nicholasgrummon/PC-Case/Pictures/Cover_Photo.jpeg

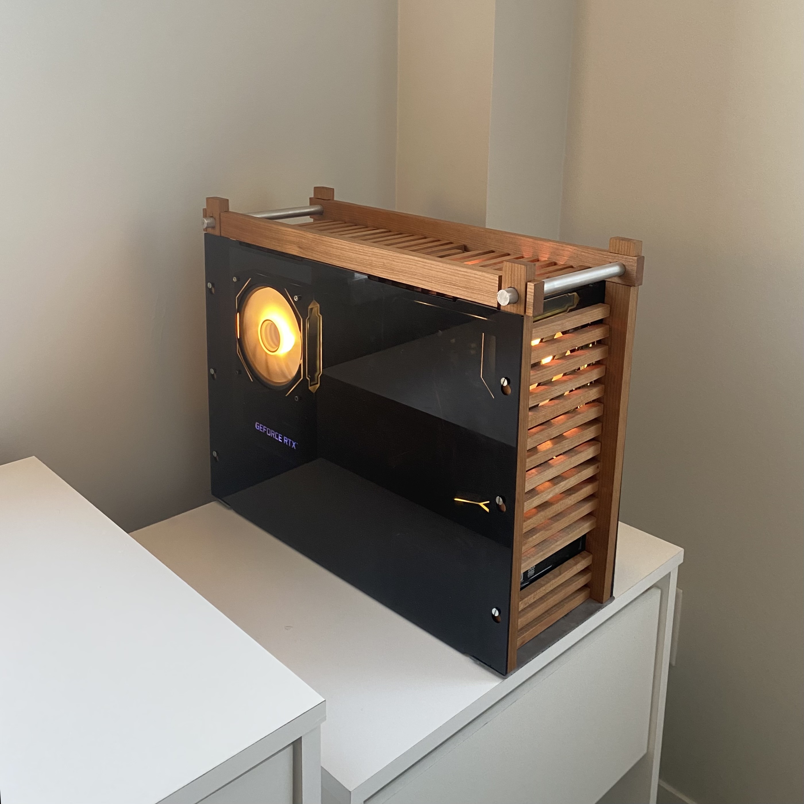
Pictures/Cover_Photo.jpeg
