nicholasgrummon/PC-Case/CADv3/PC-Case3.SLDASM

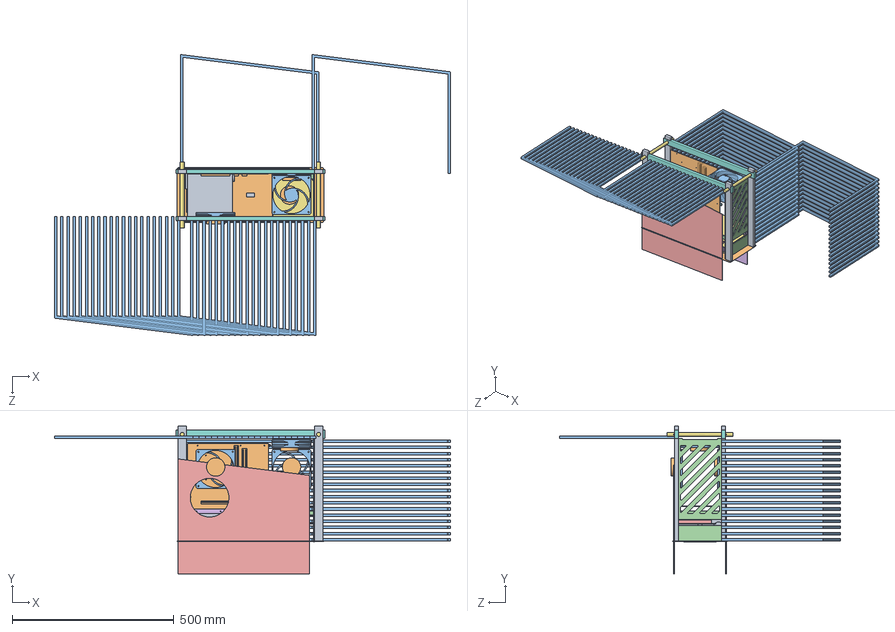
[picture p3: CAD file, 2026-05-30]
CADv3/PC-Case3.SLDASM
1225.5 x 457.2 x 869.7 mm
Base-plate
Frame-upright x 4
Frame-across x 2
Handle-rod x 2
Back-panel
Front-panel
Interface-panel
Wood-slat x 55
Motherboard
PSU
Bracket-across x 2
Hardware-Tray x 4
Hard-drive
SSD
CD-Drive
FAN BODY x 3
FAN BLADES x 3
GPU-support
