nicholasgrummon/PC-Case/CADv2/Frame-mock.SLDASM

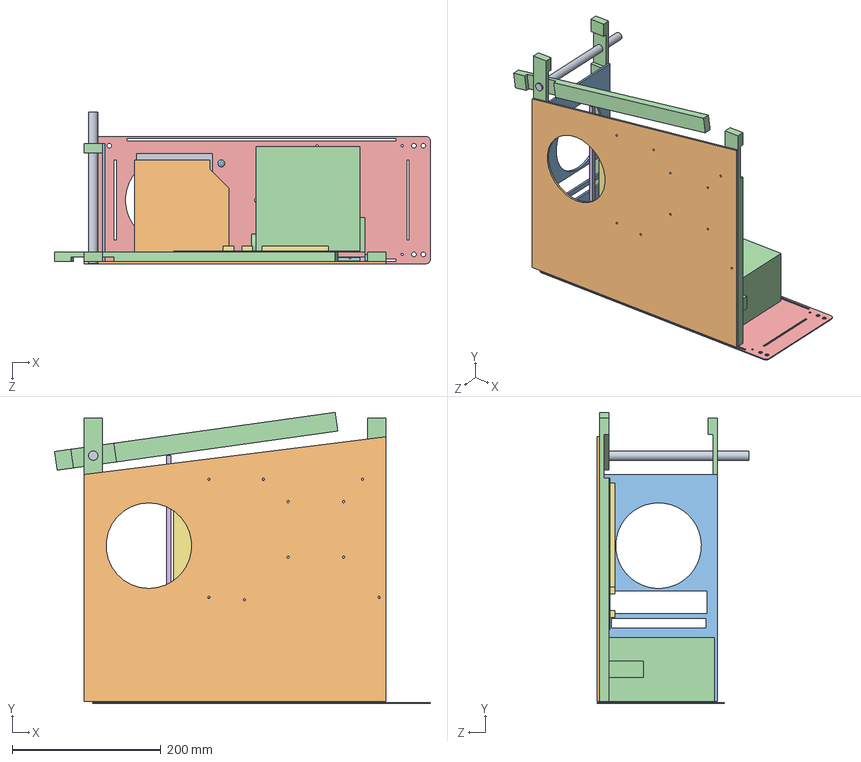
[picture p4: CAD file, 2026-05-30]
CADv2/Frame-mock.SLDASM
505.4 x 391.6 x 203.9 mm
Base-plate
Corner-slat x 4
Short-panel
Back-panel
Handle
Lbracket-short
Motherboard
Motherboard-upright-bracket x 2
Motherboard-across-bracket x 2
PSU
GPU-Post
CD-Drive
Hard-drive
