nicholasgrummon/PC-Case/CADv1/PC-Case.SLDASM

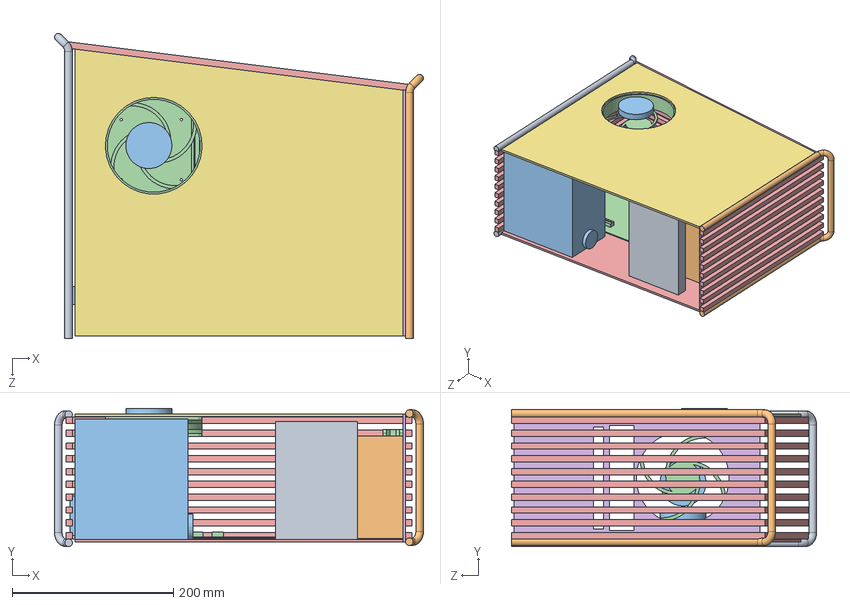
[picture p5: CAD file, 2026-05-30]
CADv1/PC-Case.SLDASM
457.3 x 171.1 x 378.3 mm
Back-panel
Motherboard
PSU
CD-Drive
Hard-drive
SSD
Front-panel
Short-panel
Wood-slat x 10
FAN BODY x 3
FAN BLADES x 3
Short-frame
Tall-frame
