nicholasgrummon/PC-Case/CADv1/Acrylic-layout.SLDASM

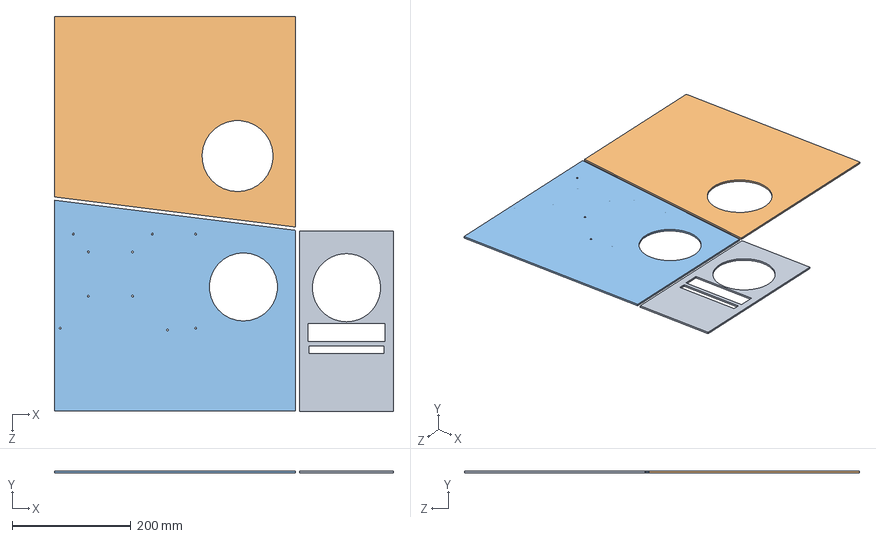
[picture p6: CAD file, 2026-05-30]
CADv1/Acrylic-layout.SLDASM
572.2 x 3.17 x 667.2 mm
Back-panel
Front-panel
Short-panel
