nicholasgrummon/PC-Case/CADv4/CPU.SLDPRT

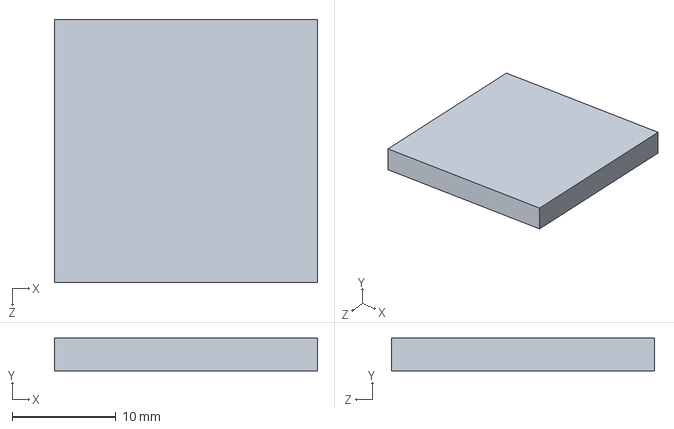
[picture p20: CAD file, 2026-05-30]
CADv4/CPU.SLDPRT
25.4 x 3.17 x 25.4 mm
