nicholasgrummon/PC-Case/CADv1/Front-panel.SLDPRT

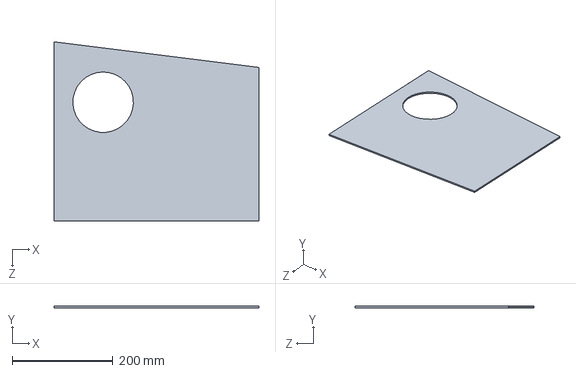
[picture p21: CAD file, 2026-05-30]
CADv1/Front-panel.SLDPRT
406.4 x 3.17 x 355.6 mm
