nicholasgrummon/PC-Case/CADv2/Motherboard-across-bracket.SLDPRT

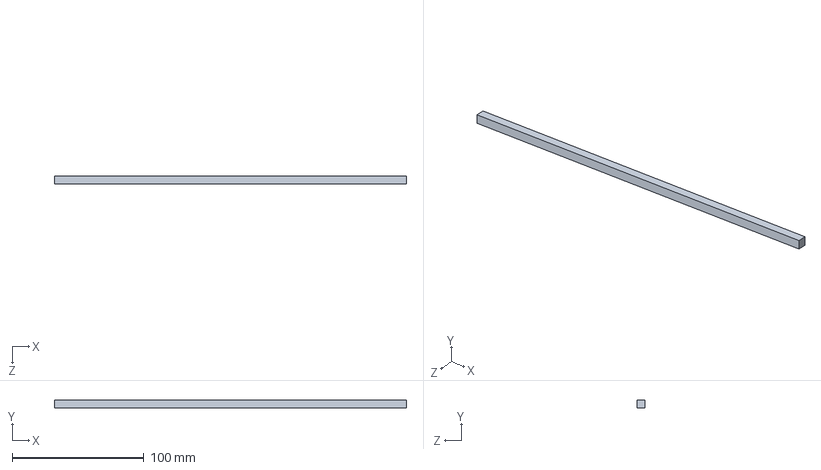
[picture p22: CAD file, 2026-05-30]
CADv2/Motherboard-across-bracket.SLDPRT
266.7 x 6.35 x 6.35 mm
