nicholasgrummon/PC-Case/CADv3/Base-plate.SLDPRT

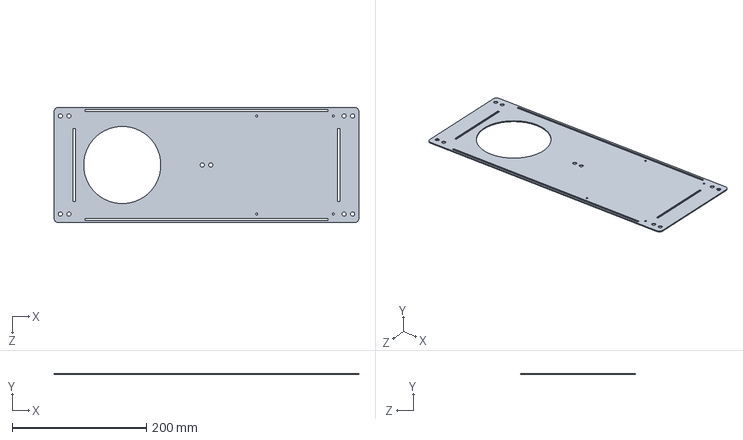
[picture p23: CAD file, 2026-05-30]
CADv3/Base-plate.SLDPRT
454.0 x 1.59 x 171.4 mm
