nicholasgrummon/PC-Case/CADv4/Unnamed-Solid001.iges

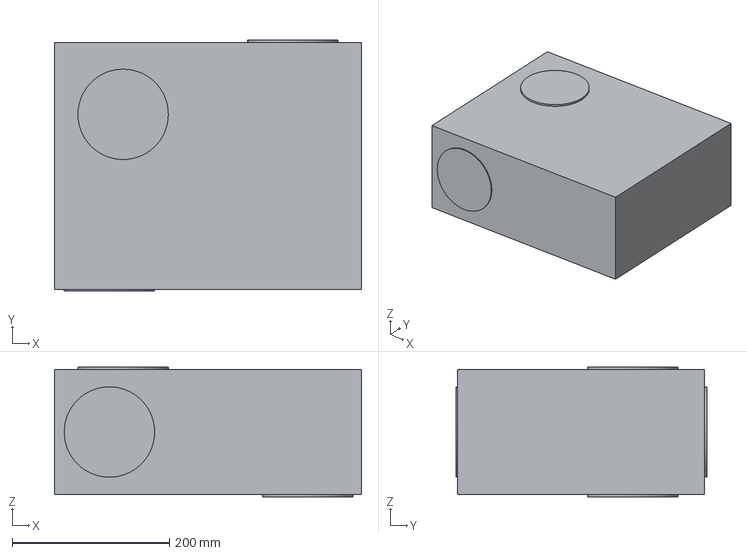
[picture p24: CAD file, 2026-05-30]
CADv4/Unnamed-Solid001.iges
390.5 x 319.1 x 165.1 mm
