nicholasgrummon/PC-Case/CADv2/GPU-Post.SLDPRT

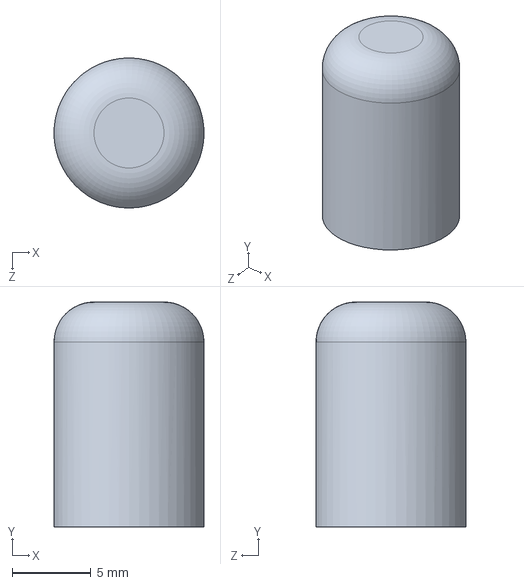
[picture p25: CAD file, 2026-05-30]
CADv2/GPU-Post.SLDPRT
9.52 x 14.3 x 9.53 mm
