nicholasgrummon/PC-Case/CADv3/GPU-support.SLDPRT

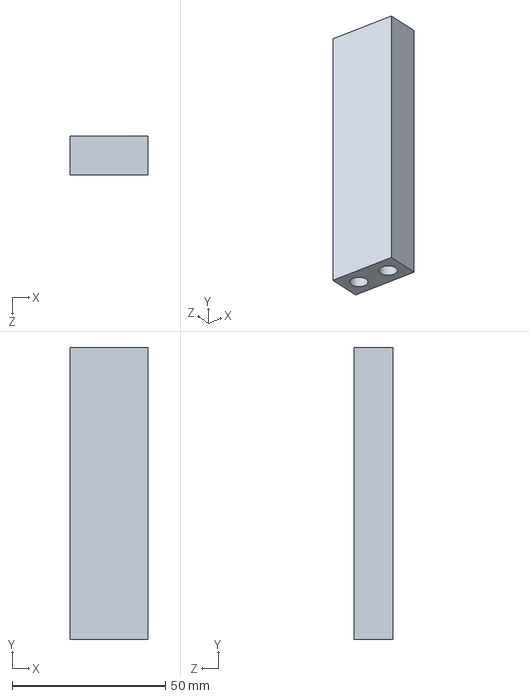
[picture p26: CAD file, 2026-05-30]
CADv3/GPU-support.SLDPRT
25.4 x 95.2 x 12.7 mm
