nicholasgrummon/PC-Case/CADv4/Back-panel-simple.SLDPRT

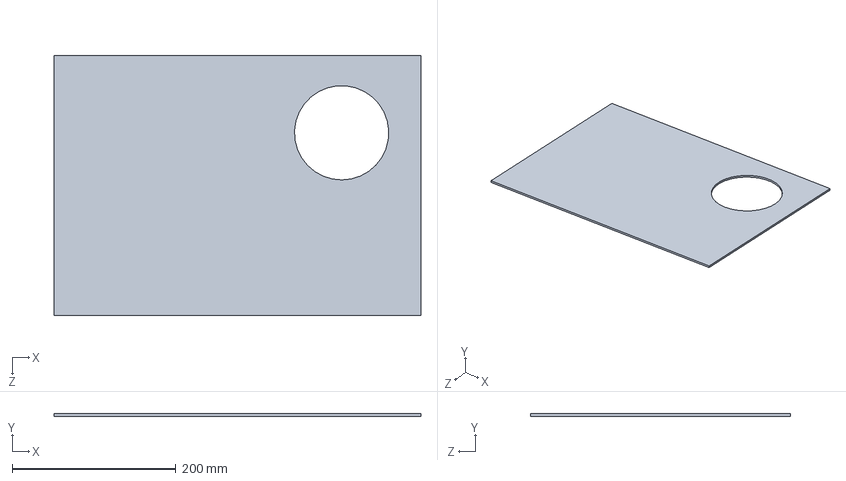
[picture p27: CAD file, 2026-05-30]
CADv4/Back-panel-simple.SLDPRT
447.7 x 3.17 x 317.5 mm
