nicholasgrummon/PC-Case/CADv1/Motherboard.SLDPRT

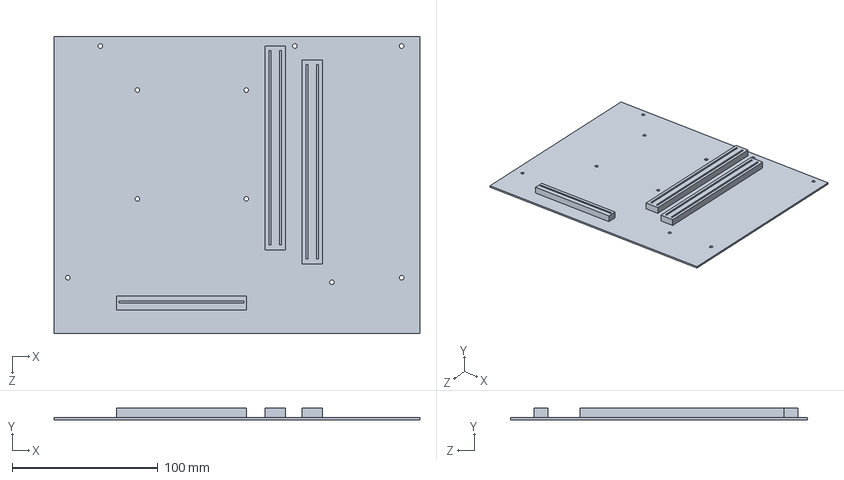
[picture p28: CAD file, 2026-05-30]
CADv1/Motherboard.SLDPRT
250.8 x 7.94 x 203.2 mm
