nicholasgrummon/PC-Case/CADv2/Wood-slat.SLDPRT

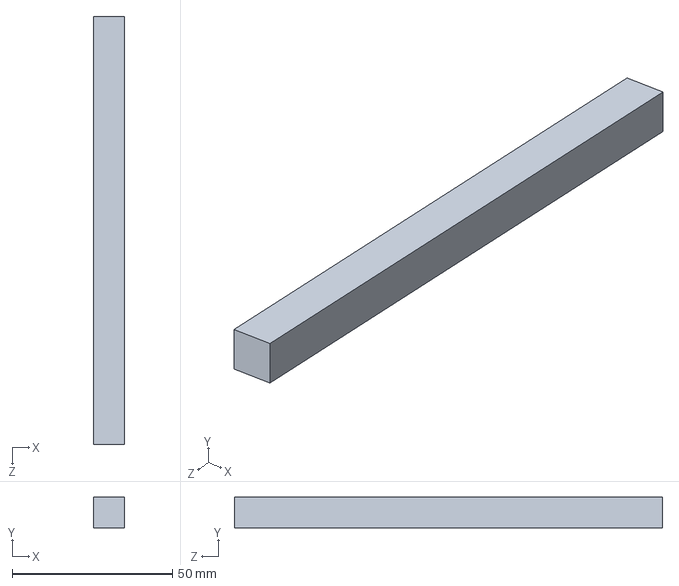
[picture p29: CAD file, 2026-05-30]
CADv2/Wood-slat.SLDPRT
9.53 x 9.53 x 133.4 mm
