nicholasgrummon/PC-Case/CADv3/Interface-panel.SLDPRT

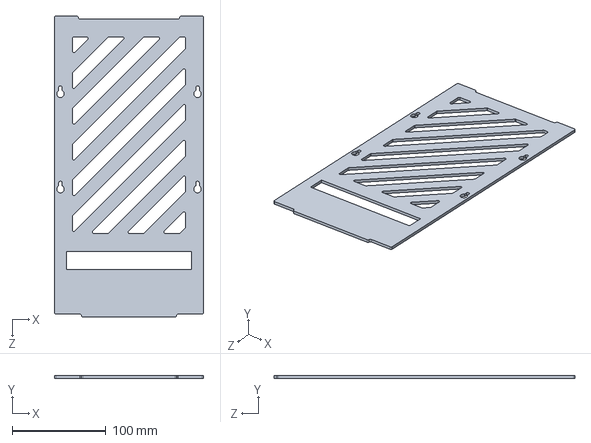
[picture p30: CAD file, 2026-05-30]
CADv3/Interface-panel.SLDPRT
158.8 x 3.17 x 320.7 mm
