nicholasgrummon/PC-Case/CADv2/Corner-slat.SLDPRT

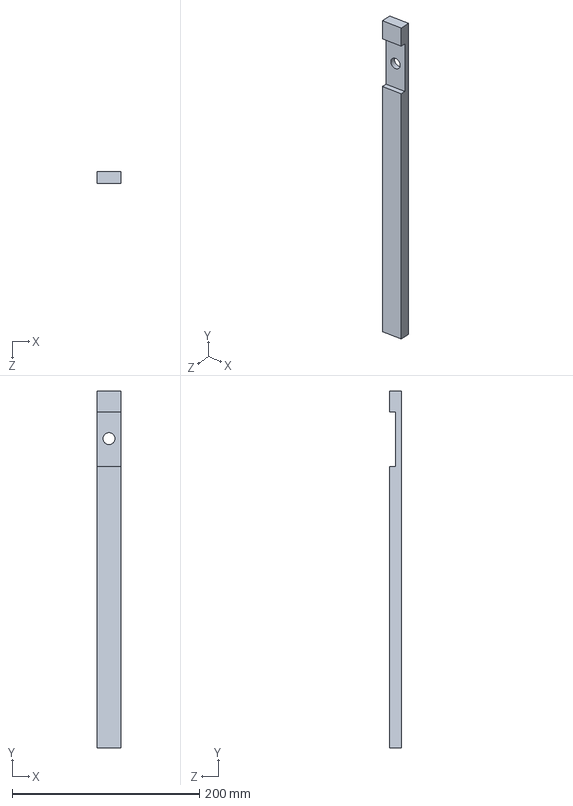
[picture p31: CAD file, 2026-05-30]
CADv2/Corner-slat.SLDPRT
25.4 x 381.0 x 12.7 mm
