nicholasgrummon/PC-Case/CADv3/Frame-across.SLDPRT

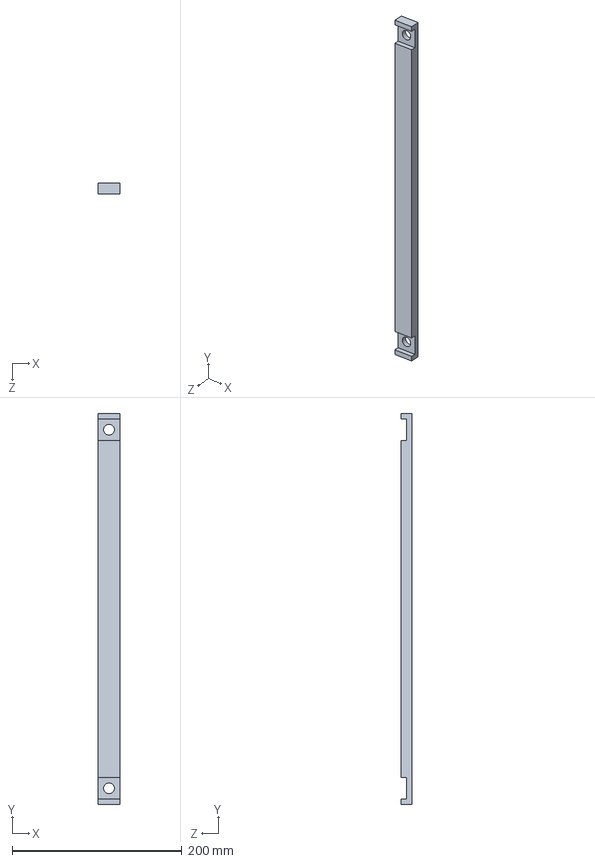
[picture p32: CAD file, 2026-05-30]
CADv3/Frame-across.SLDPRT
25.4 x 460.4 x 12.7 mm
