nicholasgrummon/PC-Case/CADv4/Frame-upright-simple.SLDPRT

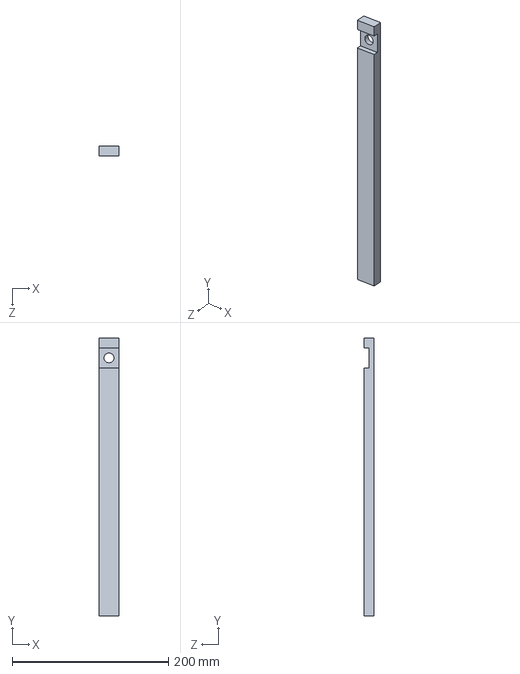
[picture p33: CAD file, 2026-05-30]
CADv4/Frame-upright-simple.SLDPRT
25.4 x 355.6 x 12.7 mm
