nicholasgrummon/PC-Case/CADv1/Short-frame.SLDPRT

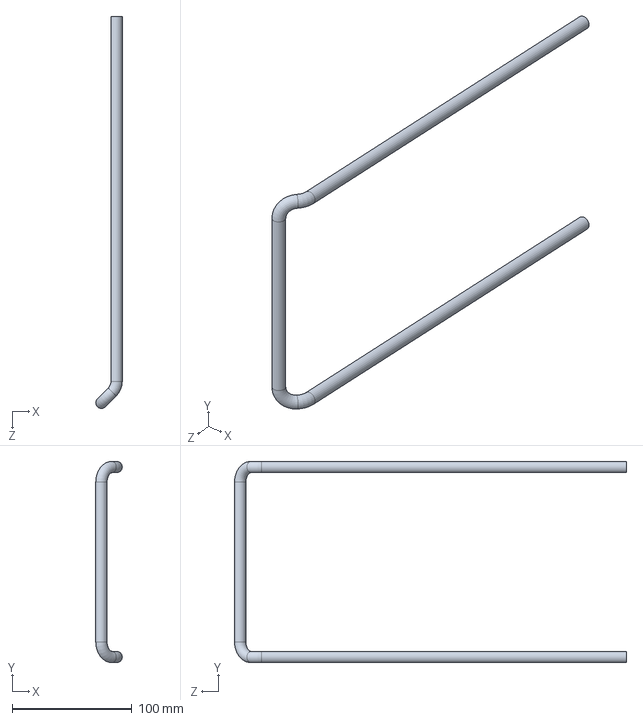
[picture p34: CAD file, 2026-05-30]
CADv1/Short-frame.SLDPRT
22.2 x 168.3 x 327.5 mm
