nicholasgrummon/PC-Case/CADv4/Air-volume.SLDPRT

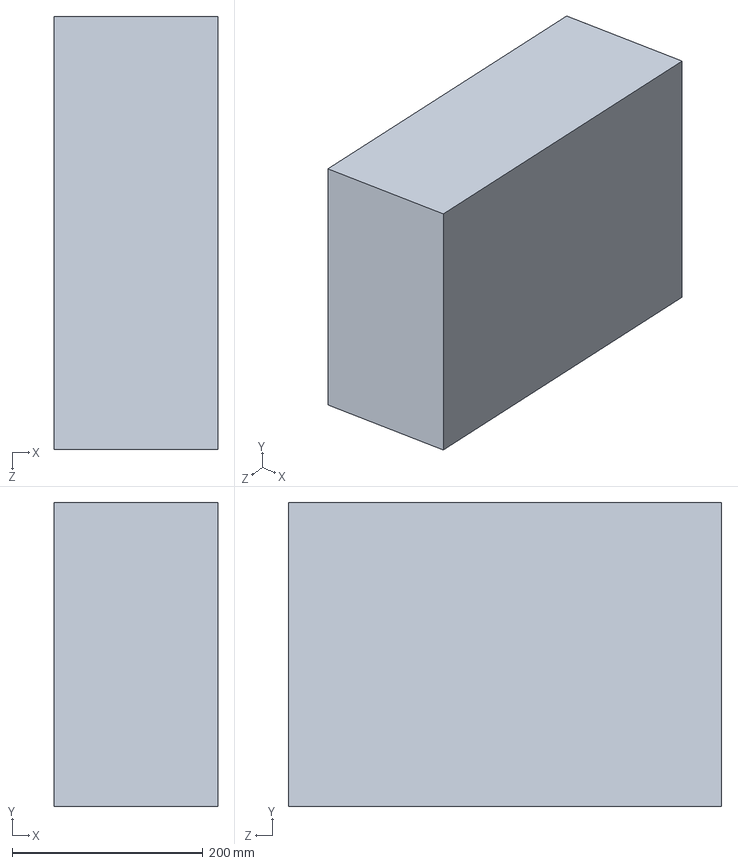
[picture p35: CAD file, 2026-05-30]
CADv4/Air-volume.SLDPRT
171.4 x 319.1 x 454.0 mm
