nicholasgrummon/PC-Case/CADv2/Hardware-Tray.SLDPRT

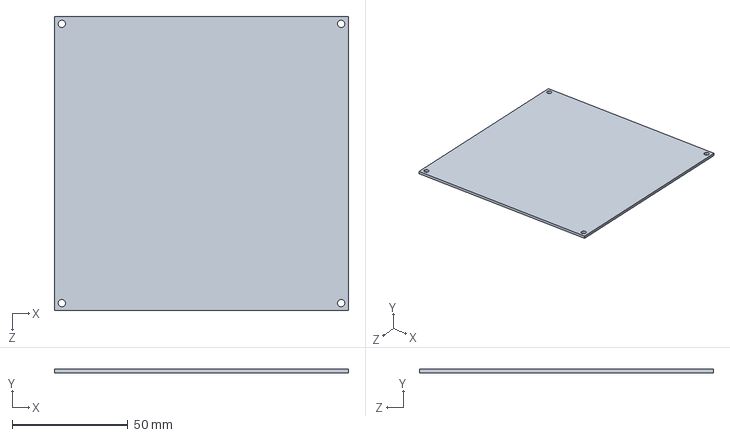
[picture p36: CAD file, 2026-05-30]
CADv2/Hardware-Tray.SLDPRT
127.0 x 1.59 x 127.0 mm
