nicholasgrummon/PC-Case/CADv2/Lbracket-short.SLDPRT

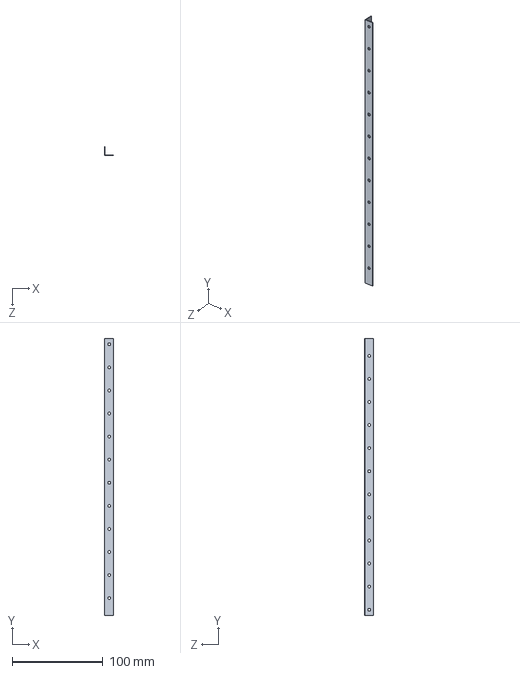
[picture p38: CAD file, 2026-05-30]
CADv2/Lbracket-short.SLDPRT
9.53 x 304.8 x 9.53 mm
