nicholasgrummon/PC-Case/CADv3/Frame-upright.SLDPRT

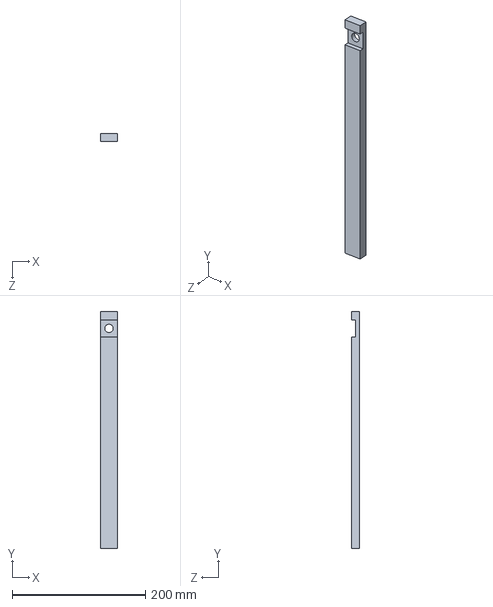
[picture p39: CAD file, 2026-05-30]
CADv3/Frame-upright.SLDPRT
25.4 x 355.6 x 12.7 mm
