nicholasgrummon/PC-Case/CADv4/PC-Case4.STEP

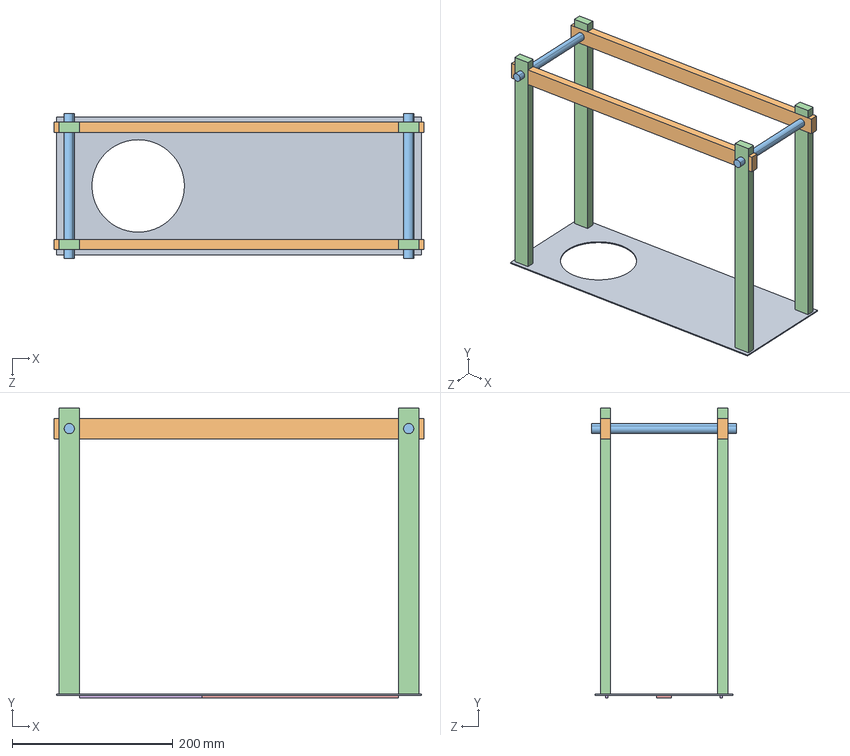
[picture p40: CAD file, 2026-05-30]
CADv4/PC-Case4.STEP
460.4 x 360.4 x 181.0 mm
Base-plate-simple
Frame-across x 2
Handle-rod-smooth x 2
Frame-upright-simple x 4
Bottom-brace
Side-brace x 2
