nicholasgrummon/PC-Case/CADv1/PSU.SLDPRT

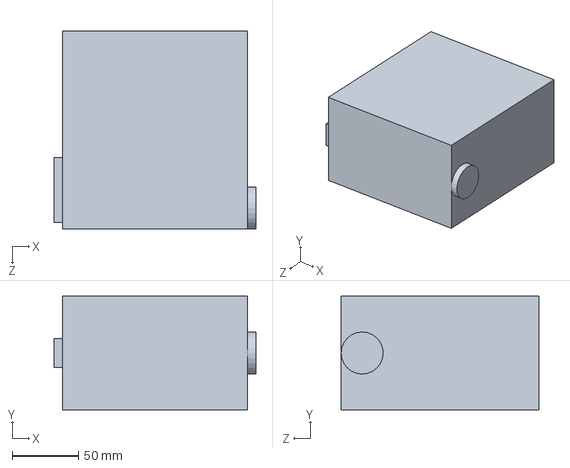
[picture p41: CAD file, 2026-05-30]
CADv1/PSU.SLDPRT
152.4 x 85.7 x 149.2 mm
