nicholasgrummon/PC-Case/CADv3/Hard-drive.SLDPRT

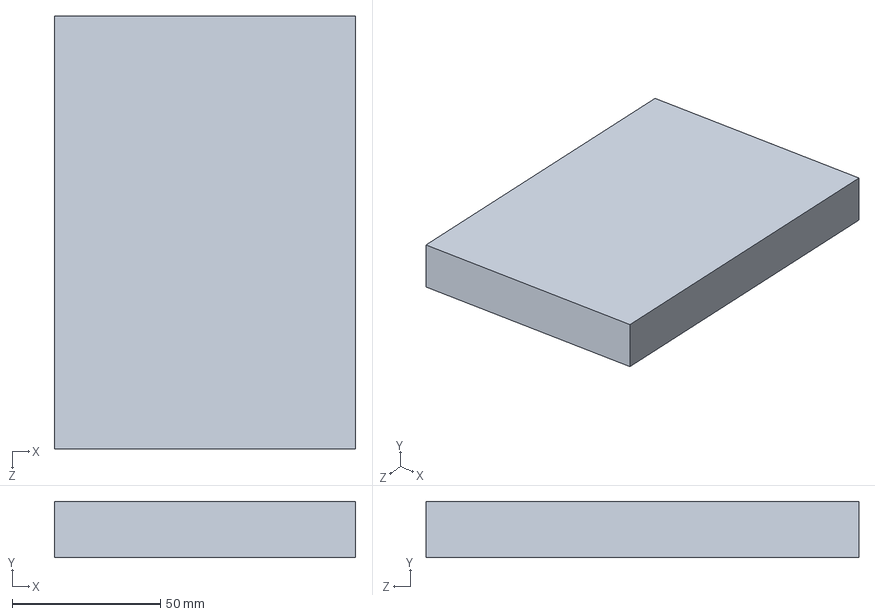
[picture p42: CAD file, 2026-05-30]
CADv3/Hard-drive.SLDPRT
101.6 x 19.1 x 146.1 mm
