nicholasgrummon/PC-Case/CADv4/Top-panel-simple.SLDPRT

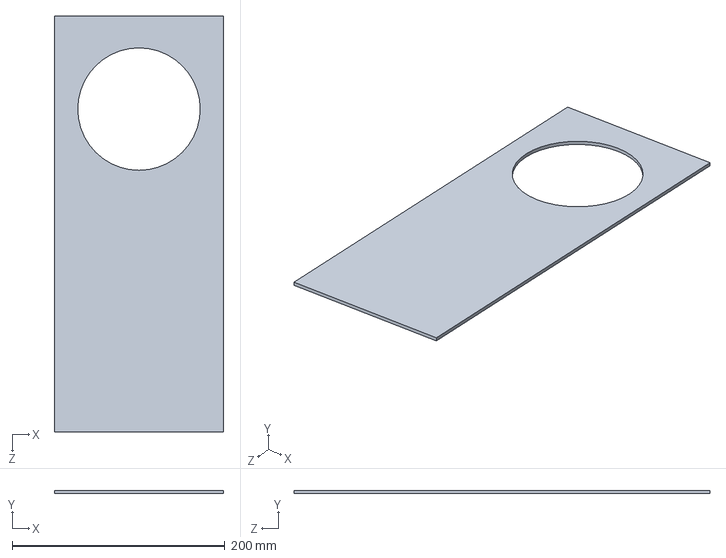
[picture p43: CAD file, 2026-05-30]
CADv4/Top-panel-simple.SLDPRT
158.8 x 3.17 x 390.5 mm
