nicholasgrummon/PC-Case/CADv3/Handle-rod.SLDPRT

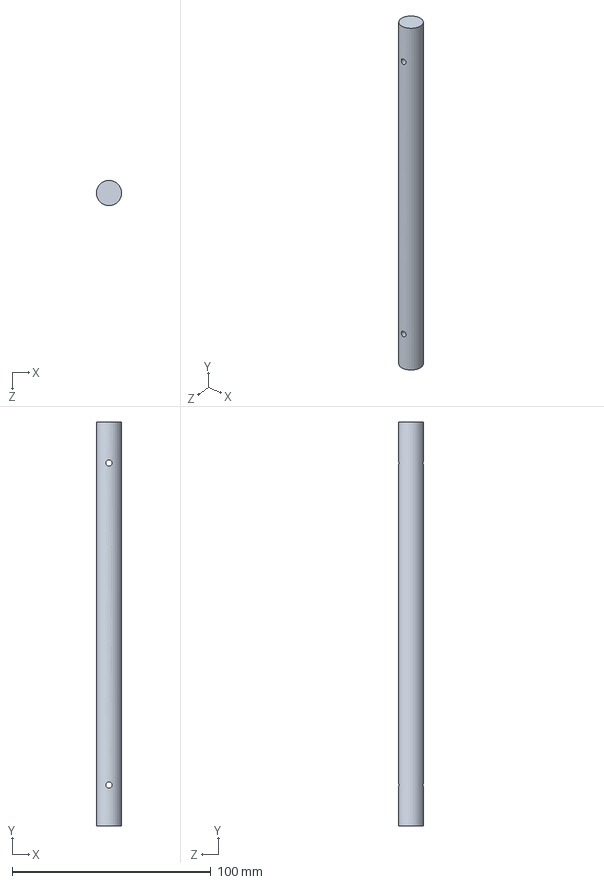
[picture p44: CAD file, 2026-05-30]
CADv3/Handle-rod.SLDPRT
12.7 x 203.2 x 12.7 mm
