nicholasgrummon/PC-Case/CADv4/Side-brace.SLDPRT

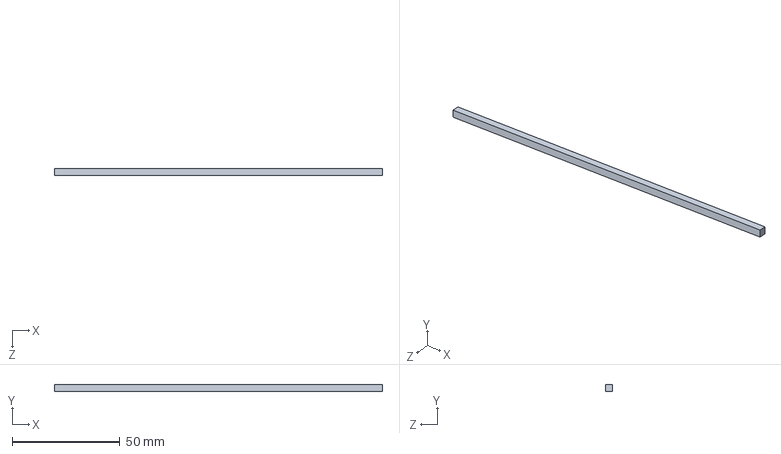
[picture p45: CAD file, 2026-05-30]
CADv4/Side-brace.SLDPRT
152.4 x 3.17 x 3.17 mm
