nicholasgrummon/PC-Case/CADv1/Short-panel.SLDPRT

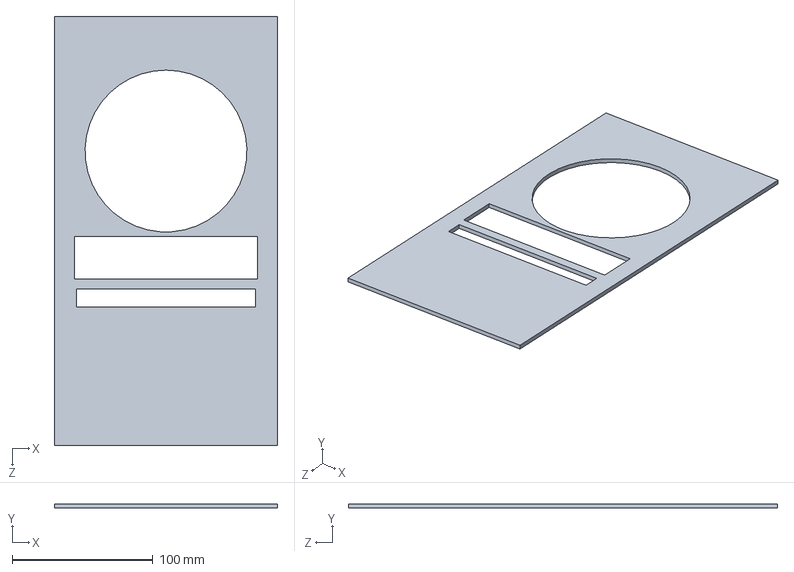
[picture p46: CAD file, 2026-05-30]
CADv1/Short-panel.SLDPRT
158.8 x 3.17 x 304.8 mm
