nicholasgrummon/PC-Case/CADv3/Port-Panel.SLDPRT

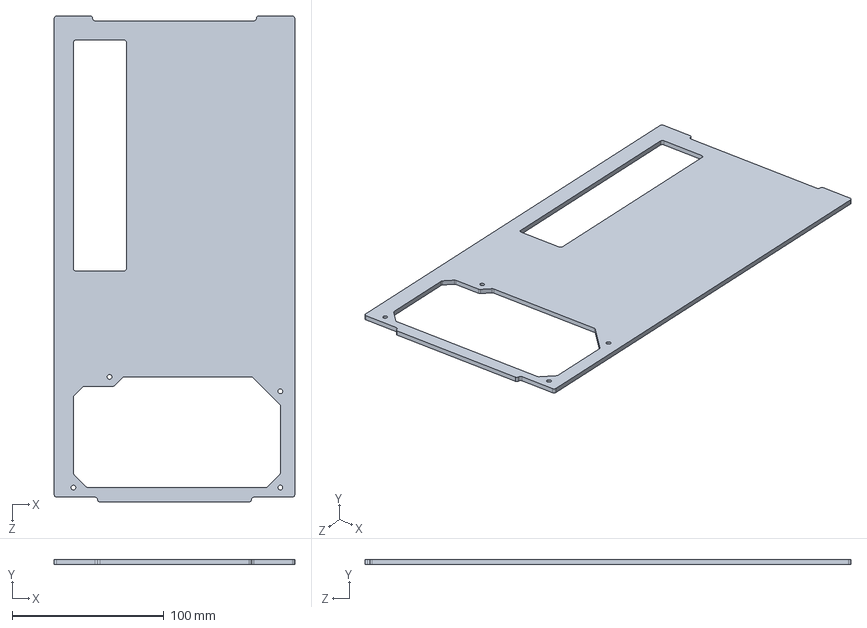
[picture p47: CAD file, 2026-05-30]
CADv3/Port-Panel.SLDPRT
158.8 x 3.17 x 320.7 mm
