nicholasgrummon/PC-Case/CADv4/Base-plate-simple.SLDPRT

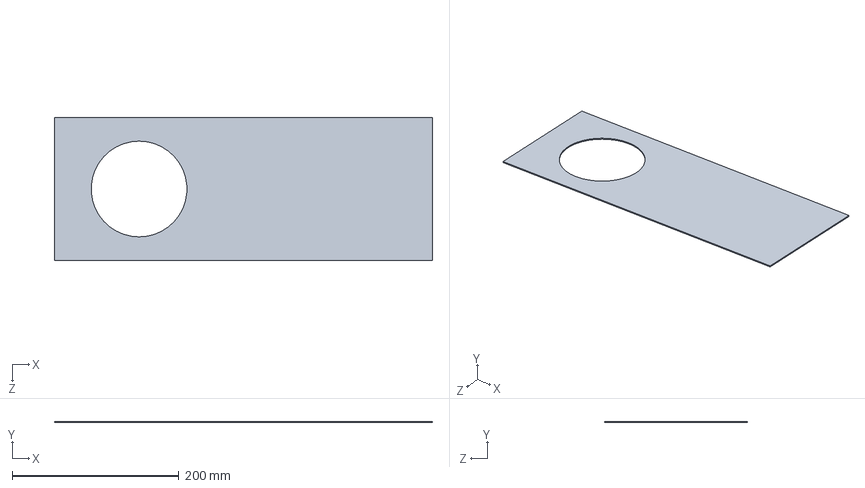
[picture p48: CAD file, 2026-05-30]
CADv4/Base-plate-simple.SLDPRT
454.0 x 1.59 x 171.4 mm
