nicholasgrummon/PC-Case/CADv1/Tall-panel.SLDPRT

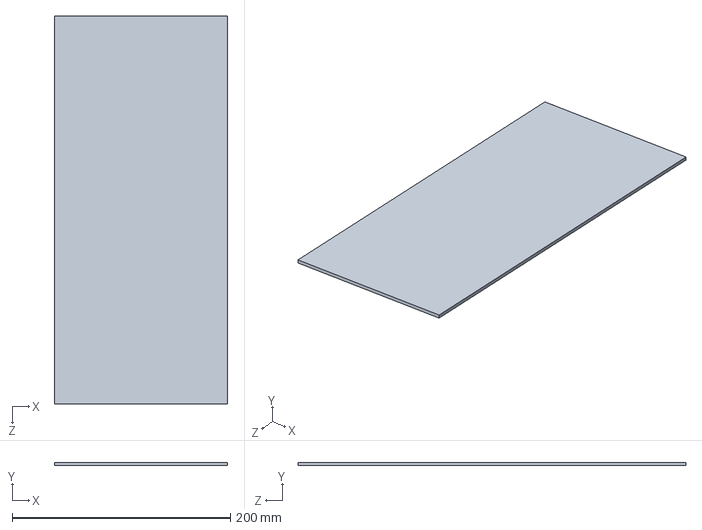
[picture p49: CAD file, 2026-05-30]
CADv1/Tall-panel.SLDPRT
158.8 x 3.17 x 355.6 mm
