nicholasgrummon/PC-Case/CADv3/Hardware-Tray.SLDPRT

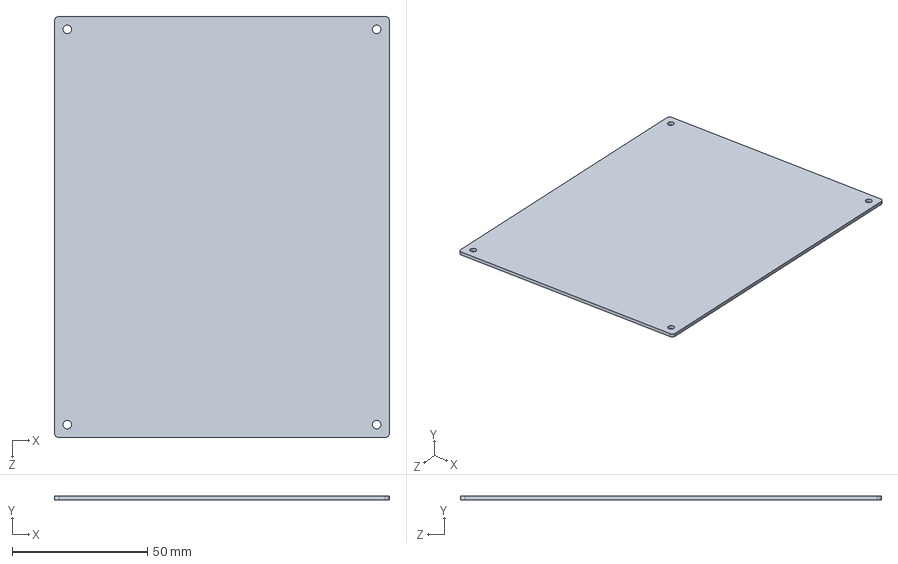
[picture p50: CAD file, 2026-05-30]
CADv3/Hardware-Tray.SLDPRT
123.8 x 1.59 x 155.6 mm
