nicholasgrummon/PC-Case/CADv4/PC-Case4-fluidmodel.STEP

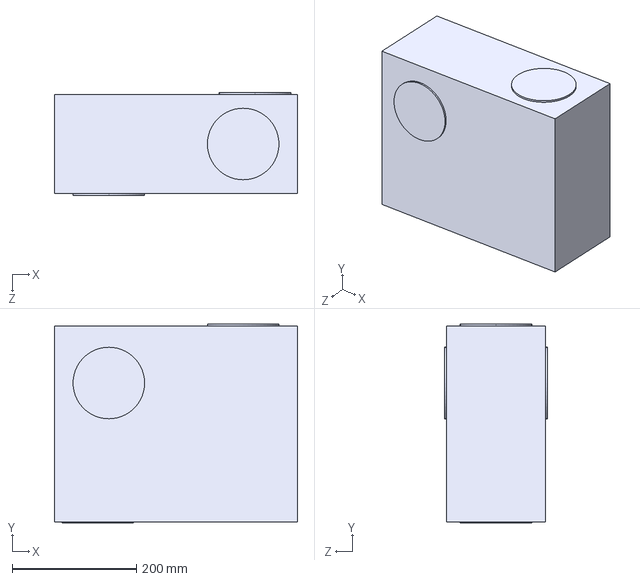
[picture p51: CAD file, 2026-05-30]
CADv4/PC-Case4-fluidmodel.STEP
390.5 x 319.1 x 165.1 mm
