nicholasgrummon/PC-Case/CADv1/Base-plate.SLDPRT

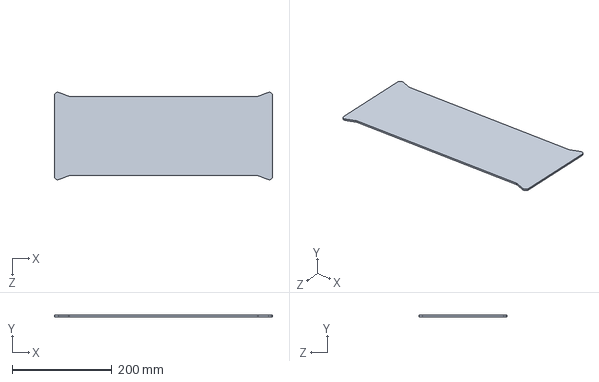
[picture p52: CAD file, 2026-05-30]
CADv1/Base-plate.SLDPRT
436.7 x 3.17 x 175.5 mm
