nicholasgrummon/PC-Case/CADv3/Bottom-brace.SLDPRT

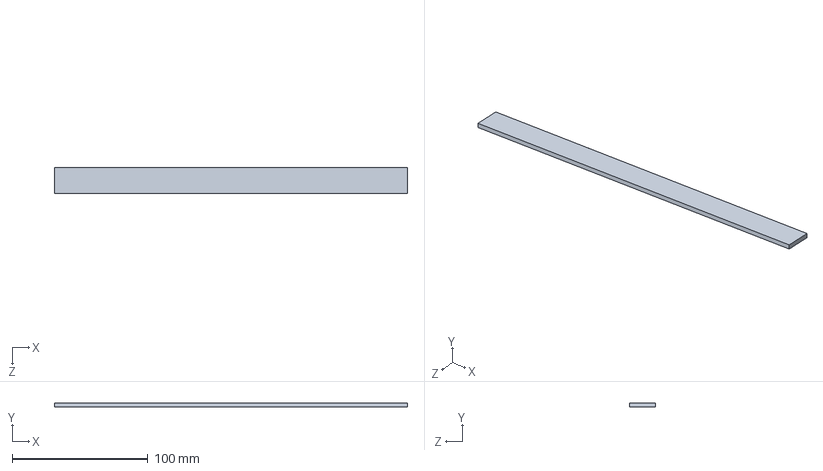
[picture p53: CAD file, 2026-05-30]
CADv3/Bottom-brace.SLDPRT
260.3 x 3.17 x 19.1 mm
