nicholasgrummon/PC-Case/CADv3/Motherboard.SLDPRT

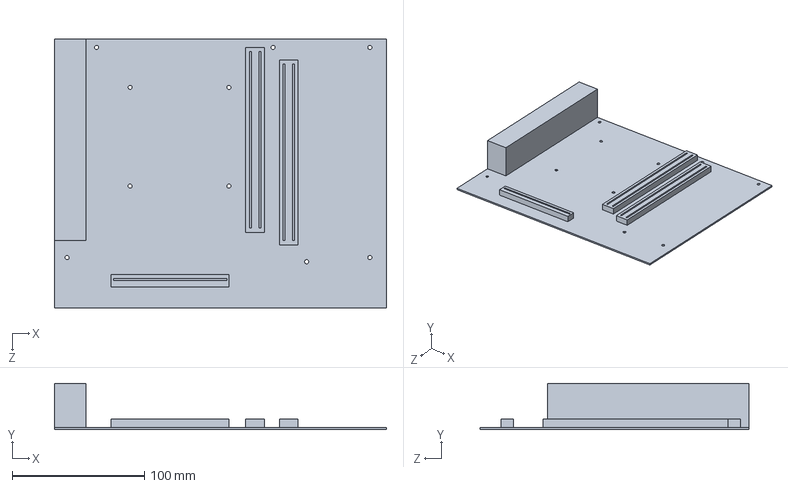
[picture p54: CAD file, 2026-05-30]
CADv3/Motherboard.SLDPRT
250.8 x 34.9 x 203.2 mm
