nicholasgrummon/PC-Case/CADv3/Title-block.SLDPRT

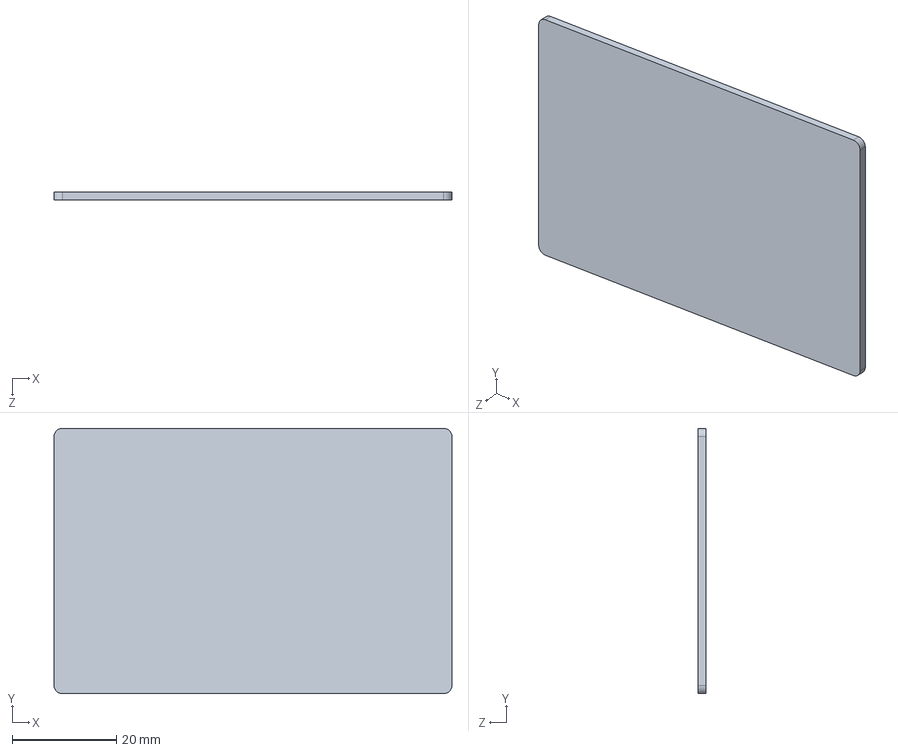
[picture p55: CAD file, 2026-05-30]
CADv3/Title-block.SLDPRT
76.2 x 50.8 x 1.59 mm
