nicholasgrummon/PC-Case/CADv3/Bracket-upright.SLDPRT

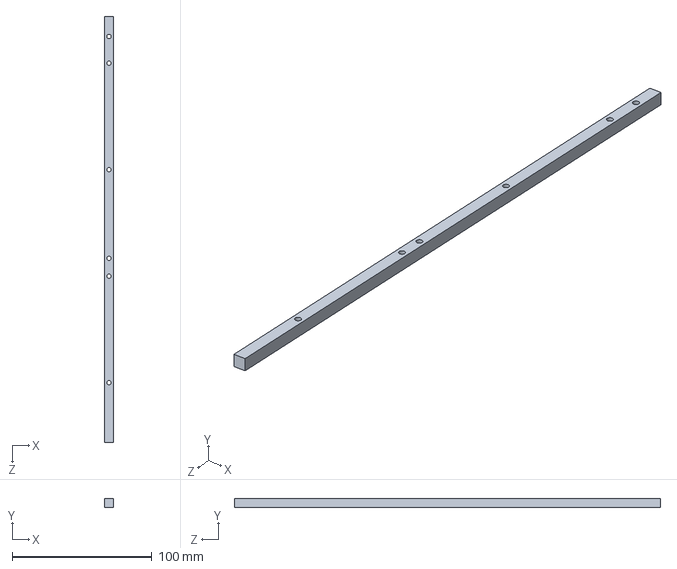
[picture p56: CAD file, 2026-05-30]
CADv3/Bracket-upright.SLDPRT
6.35 x 6.35 x 304.8 mm
