nicholasgrummon/PC-Case/CADv3/Top-panel.SLDPRT

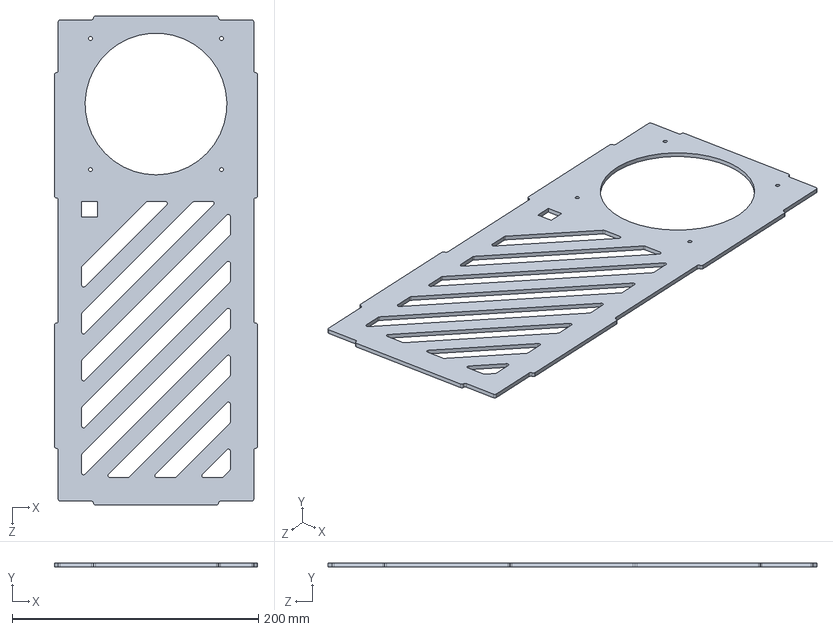
[picture p57: CAD file, 2026-05-30]
CADv3/Top-panel.SLDPRT
165.1 x 3.17 x 396.9 mm
