nicholasgrummon/PC-Case/CADv3/Standoff.SLDPRT

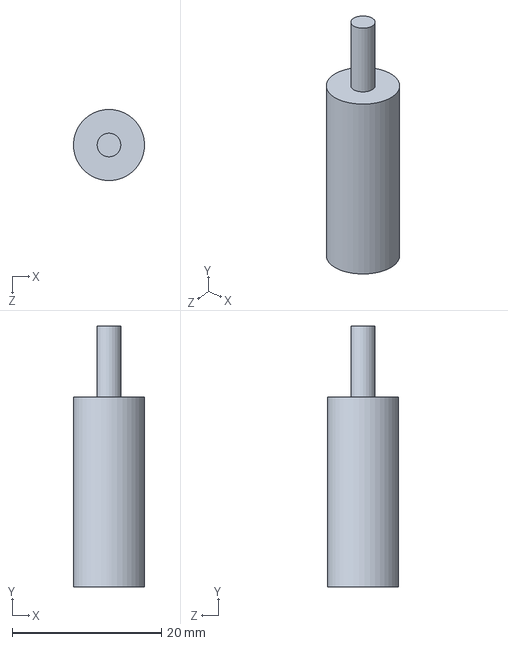
[picture p58: CAD file, 2026-05-30]
CADv3/Standoff.SLDPRT
9.52 x 34.9 x 9.53 mm
