nicholasgrummon/PC-Case/CADv3/RAM-Card.SLDPRT

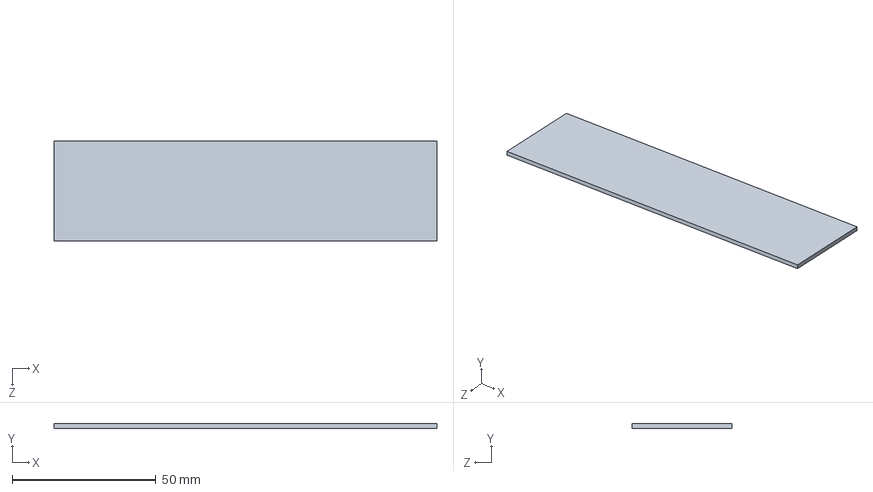
[picture p59: CAD file, 2026-05-30]
CADv3/RAM-Card.SLDPRT
133.4 x 1.59 x 34.9 mm
