nicholasgrummon/PC-Case/CADv3/GPU.SLDPRT

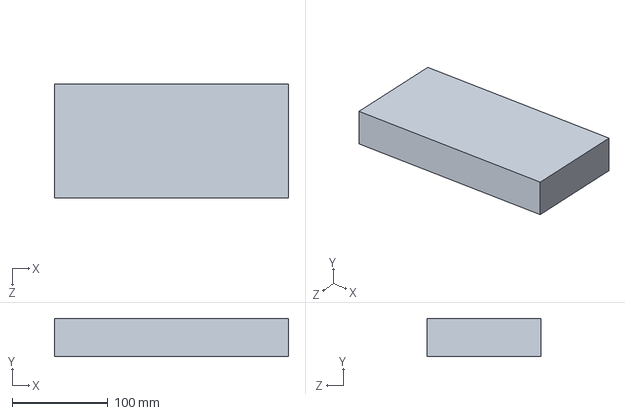
[picture p60: CAD file, 2026-05-30]
CADv3/GPU.SLDPRT
245.0 x 40.0 x 119.0 mm
